phil31/NerdEKO-Gamma/images/IMG_20241215_021152095.jpg

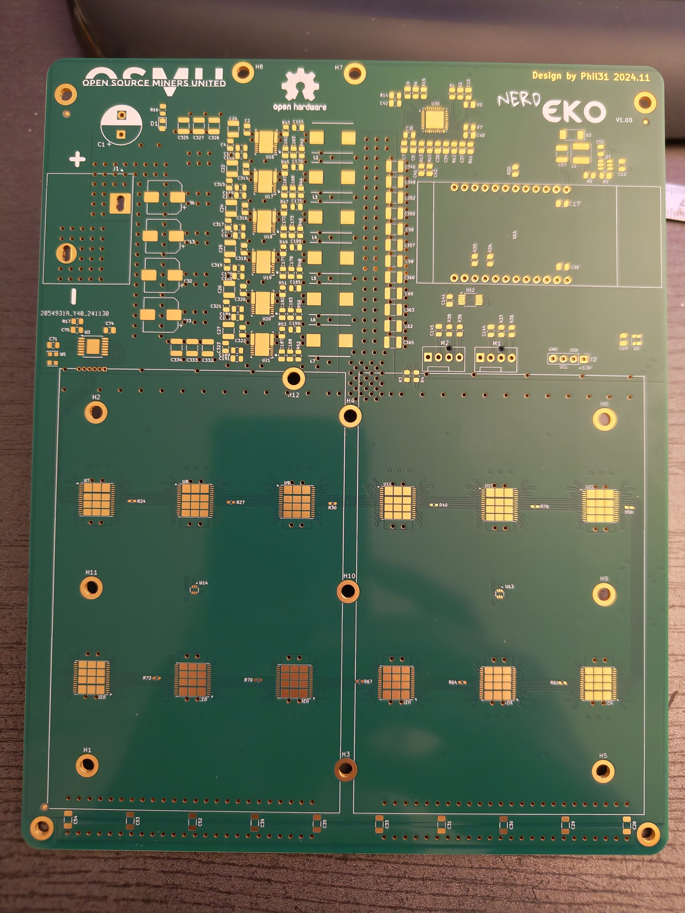
images/IMG_20241215_021152095.jpg
