phil31/NerdEKO-Gamma/images/IMG_20250128_200442238.jpg

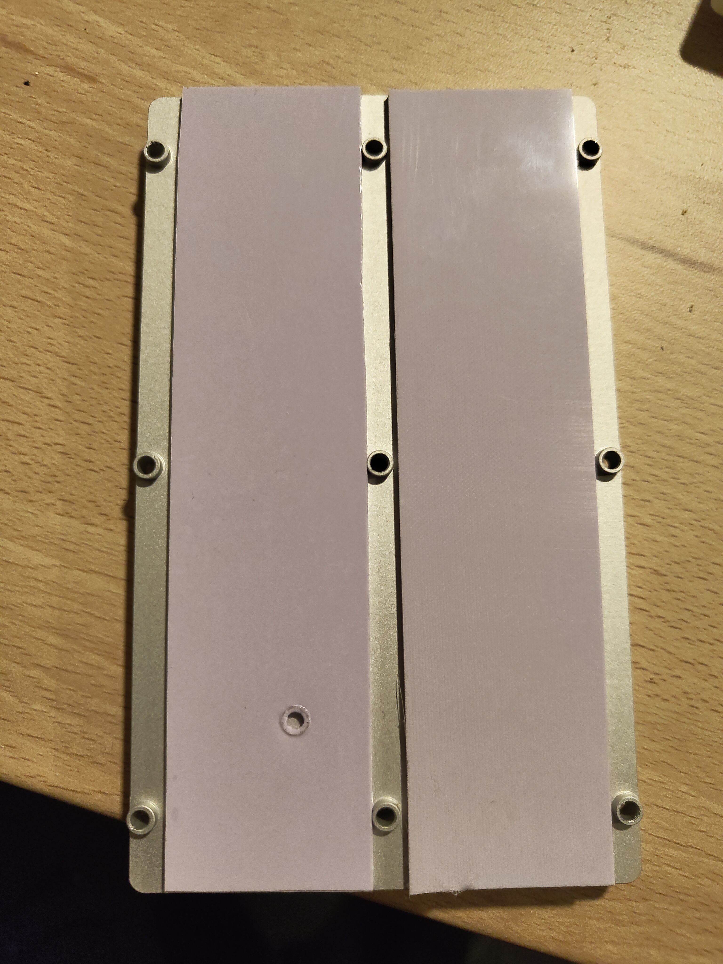
images/IMG_20250128_200442238.jpg
