phil31/NerdEKO-Gamma/images/IMG_20250128_201800067.jpg

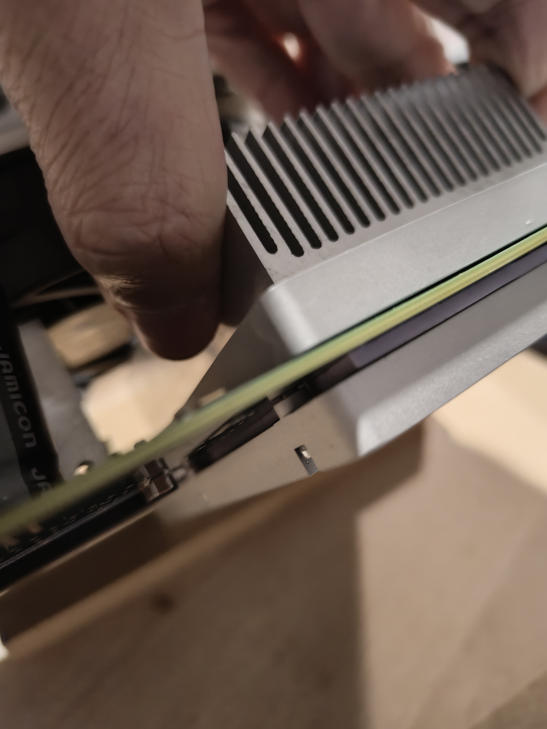
images/IMG_20250128_201800067.jpg
