phil31/NerdEKO-Gamma/images/IMG_20250130_210807385.jpg

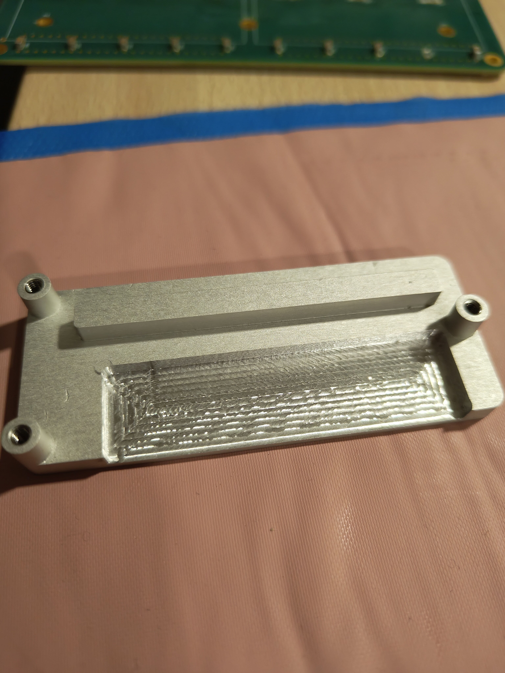
images/IMG_20250130_210807385.jpg
