phil31/NerdEKO-Gamma/images/IMG_20250130_211350961.jpg

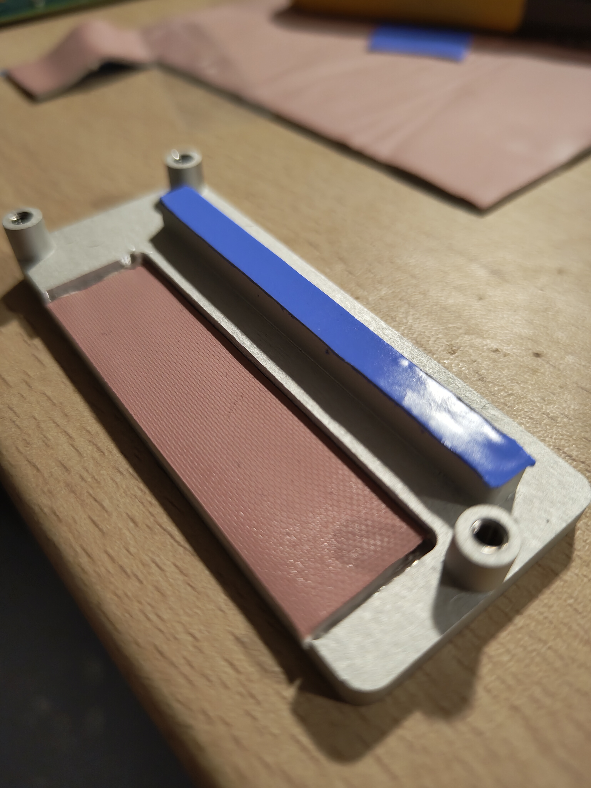
images/IMG_20250130_211350961.jpg
