phil31/NerdEKO-Gamma/images/IMG_20250316_115821073.jpg

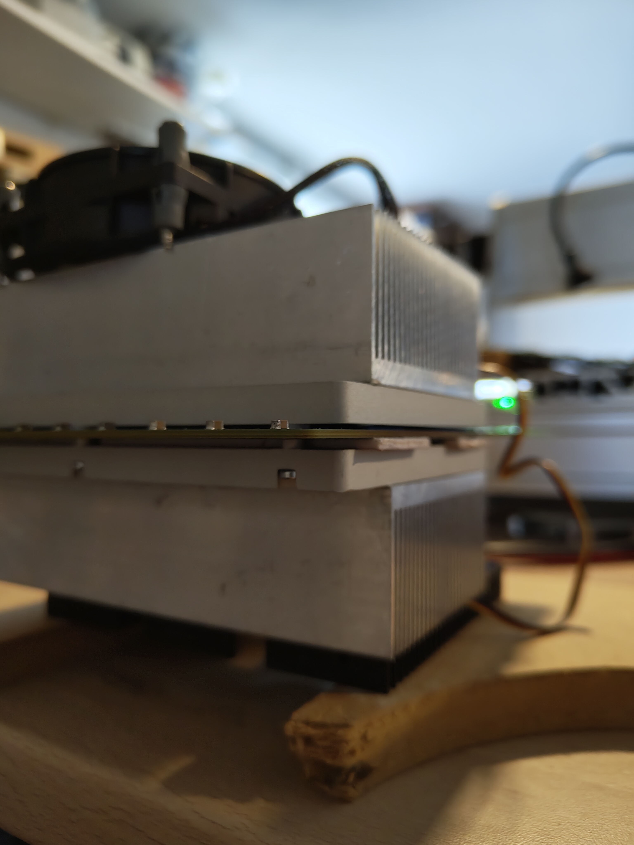
images/IMG_20250316_115821073.jpg
