phil31/NerdEKO-Gamma/images/IMG_20250322_192944470.jpg

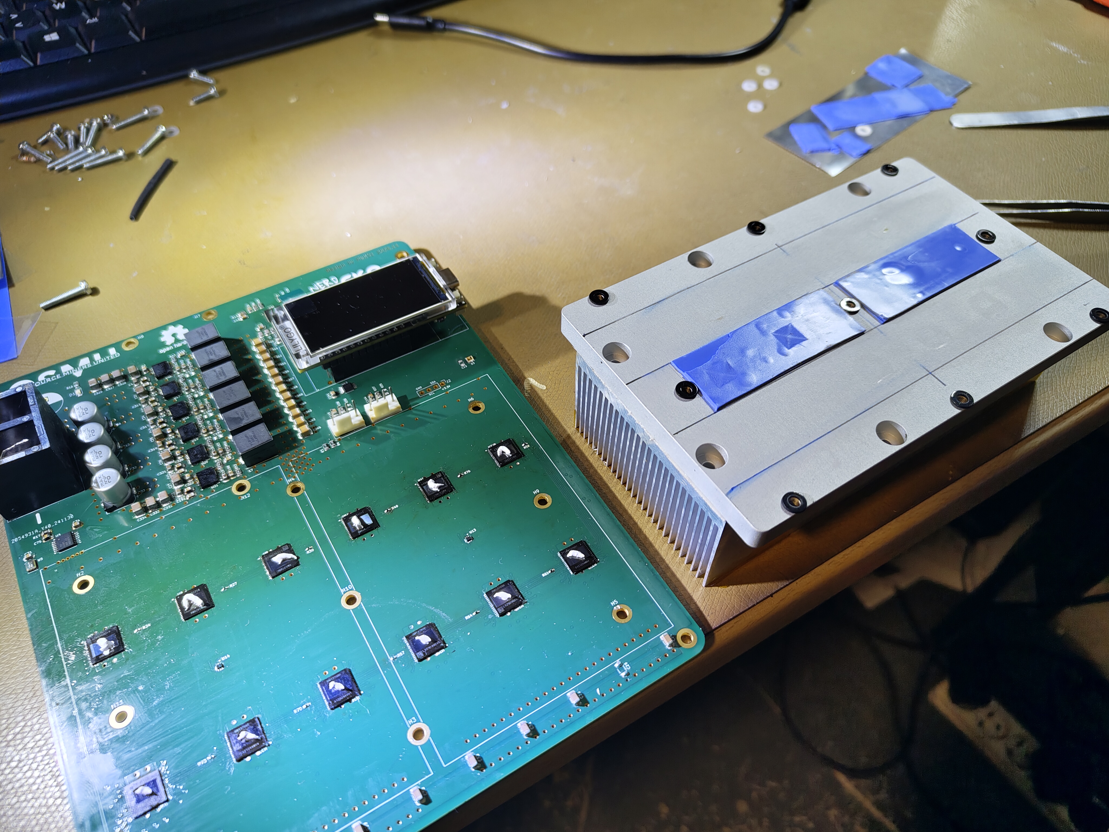
images/IMG_20250322_192944470.jpg
