phil31/NerdEKO-Gamma/images/IMG_20250322_193003022.jpg

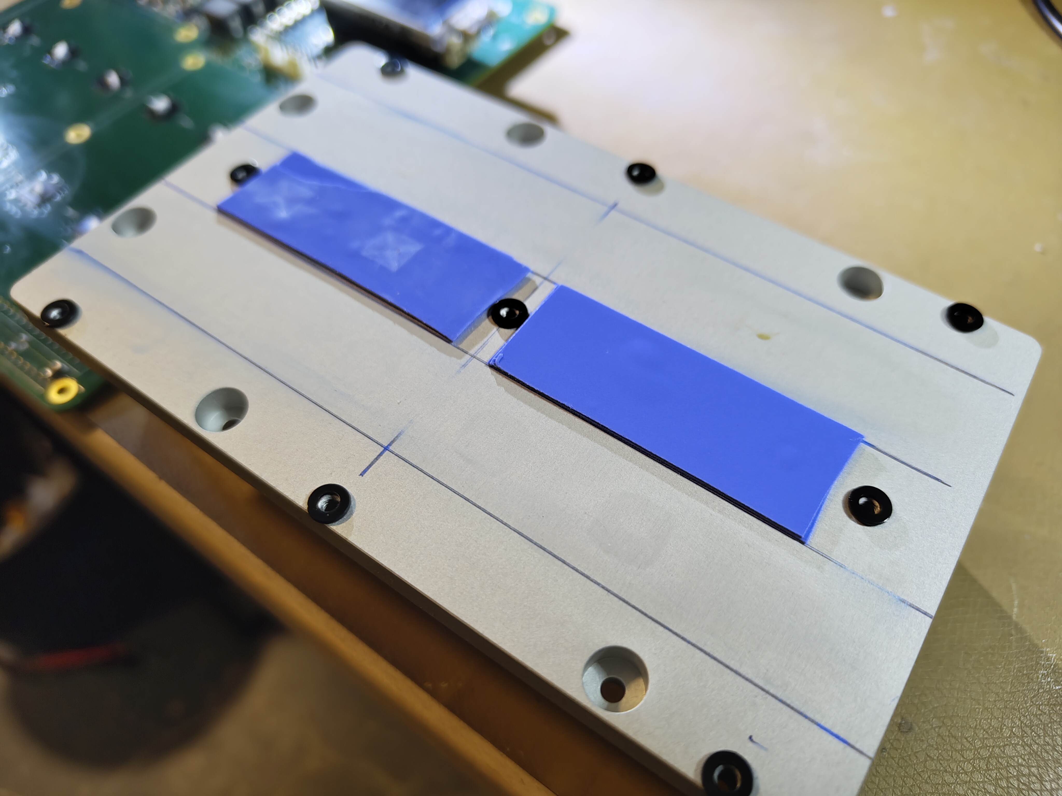
images/IMG_20250322_193003022.jpg
