phil31/NerdEKO-Gamma/images/IMG_20250331_194657219.jpg

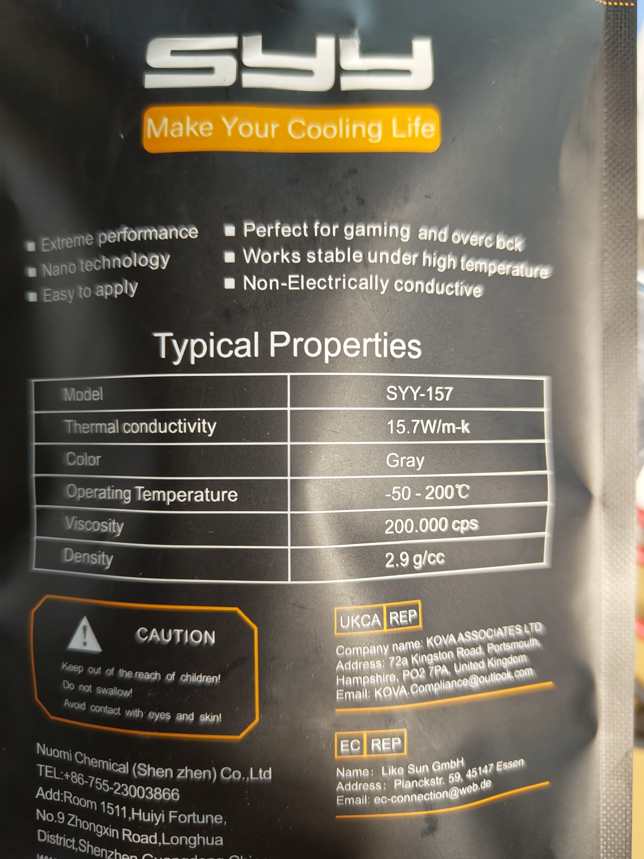
images/IMG_20250331_194657219.jpg
