phil31/NerdEKO-Gamma/images/IMG_20250303_195049834.jpg

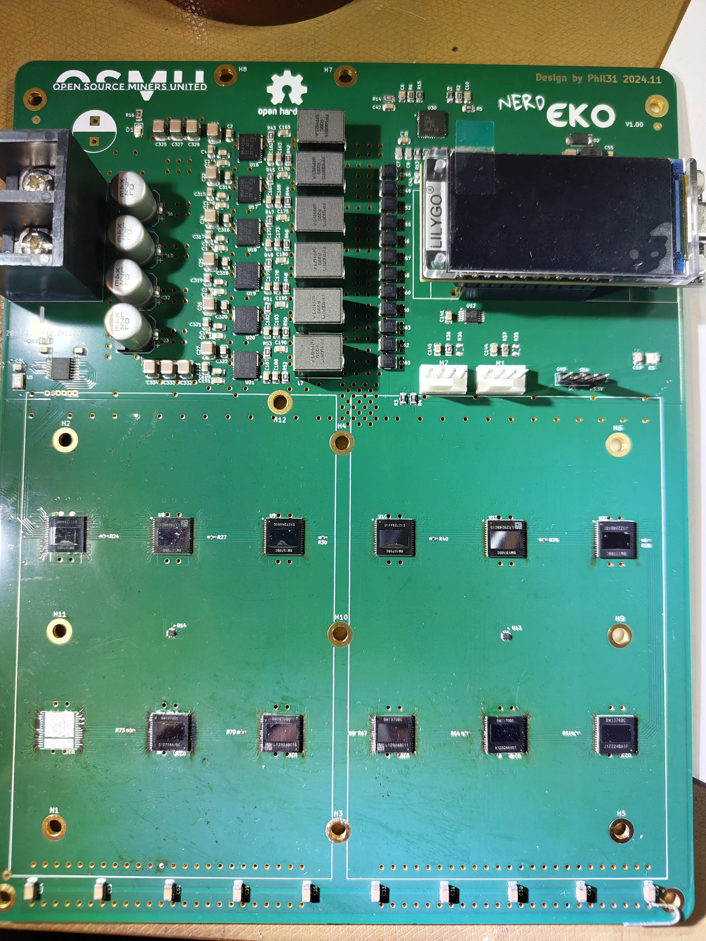
images/IMG_20250303_195049834.jpg
